dpnebert/Dura-M3000/firmware/components/dura_board/dura_lcd_assets.c

// Generated from Dura legacy MikroBasic reference assets.
// Source directory: /home/omi/work_projects/dura/AVR/reference_source/Release_1_1_3/Src/Meter_Project
// Do not hand-edit byte data; regenerate from the reference source if assets change.

#include "dura_lcd_assets.h"

// Source: Graphics.mbas const QRcodeData as byte[((128*64)/8)] (1024 values)
const uint8_t dura_asset_QRcodeData[1024] = {
    0x00u, 0x00u, 0x00u, 0x00u, 0x00u, 0x00u, 0x00u, 0x00u, 0x00u, 0x00u, 0x00u, 0x00u, 0x00u, 0x00u, 0x00u, 0x00u,
    0x00u, 0x00u, 0x00u, 0x00u, 0x00u, 0x00u, 0x00u, 0x00u, 0x00u, 0x00u, 0x00u, 0x00u, 0x00u, 0x00u, 0x00u, 0x00u,
    0x00u, 0x00u, 0x00u, 0x00u, 0x00u, 0x00u, 0x00u, 0x80u, 0x80u, 0x80u, 0x80u, 0x80u, 0x80u, 0x80u, 0x80u, 0x80u,
    0x80u, 0x80u, 0x80u, 0x80u, 0x80u, 0x00u, 0x00u, 0x80u, 0x80u, 0x80u, 0x80u, 0x80u, 0x80u, 0x00u, 0x00u, 0x00u,
    0x00u, 0x80u, 0x80u, 0x00u, 0x00u, 0x00u, 0x00u, 0x00u, 0x00u, 0x00u, 0x00u, 0x80u, 0x80u, 0x80u, 0x80u, 0x80u,
    0x80u, 0x80u, 0x80u, 0x80u, 0x80u, 0x80u, 0x80u, 0x80u, 0x80u, 0x00u, 0x00u, 0x00u, 0x00u, 0x00u, 0x00u, 0x00u,
    0x00u, 0x00u, 0x00u, 0x00u, 0x00u, 0x00u, 0x00u, 0x00u, 0x00u, 0x00u, 0x00u, 0x00u, 0x00u, 0x00u, 0x00u, 0x00u,
    0x00u, 0x00u, 0x00u, 0x00u, 0x00u, 0x00u, 0x00u, 0x00u, 0x00u, 0x00u, 0x00u, 0x00u, 0x00u, 0x00u, 0x00u, 0x00u,
    0x00u, 0x00u, 0x00u, 0x00u, 0x00u, 0x00u, 0x00u, 0x00u, 0x00u, 0x00u, 0x00u, 0x00u, 0x00u, 0x00u, 0x00u, 0x00u,
    0x00u, 0x00u, 0x00u, 0x00u, 0x00u, 0x00u, 0x00u, 0x00u, 0x00u, 0x00u, 0x00u, 0x00u, 0x00u, 0x00u, 0x00u, 0x00u,
    0x00u, 0x00u, 0x00u, 0x00u, 0x00u, 0x00u, 0x00u, 0xFFu, 0xFFu, 0x01u, 0x01u, 0xF9u, 0xF9u, 0xF9u, 0xF9u, 0xF9u,
    0xF9u, 0x01u, 0x01u, 0xFFu, 0xFFu, 0x00u, 0x00u, 0x01u, 0x01u, 0xF9u, 0xF9u, 0x1Fu, 0x1Fu, 0x78u, 0x78u, 0x60u,
    0x60u, 0x7Fu, 0x7Fu, 0x00u, 0x00u, 0x00u, 0x00u, 0xFEu, 0xFEu, 0x00u, 0x00u, 0xFFu, 0xFFu, 0x01u, 0x01u, 0xF9u,
    0xF9u, 0xF9u, 0xF9u, 0xF9u, 0xF9u, 0x01u, 0x01u, 0xFFu, 0xFFu, 0x00u, 0x00u, 0x00u, 0x00u, 0x00u, 0x00u, 0x00u,
    0x00u, 0x00u, 0x00u, 0x00u, 0x00u, 0x00u, 0x00u, 0x00u, 0x00u, 0x00u, 0x00u, 0x00u, 0x00u, 0x00u, 0x00u, 0x00u,
    0x00u, 0x00u, 0x00u, 0x00u, 0x00u, 0x00u, 0x00u, 0x00u, 0x00u, 0x00u, 0x00u, 0x00u, 0x00u, 0x00u, 0x00u, 0x00u,
    0x00u, 0x00u, 0x00u, 0x00u, 0x00u, 0x00u, 0x00u, 0x00u, 0x00u, 0x00u, 0x00u, 0x00u, 0x00u, 0x00u, 0x00u, 0x00u,
    0x00u, 0x00u, 0x00u, 0x00u, 0x00u, 0x00u, 0x00u, 0x00u, 0x00u, 0x00u, 0x00u, 0x00u, 0x00u, 0x00u, 0x00u, 0x00u,
    0x00u, 0x00u, 0x00u, 0x00u, 0x00u, 0x00u, 0x00u, 0x9Fu, 0x9Fu, 0x98u, 0x98u, 0x19u, 0x19u, 0x99u, 0x99u, 0x99u,
    0x99u, 0x18u, 0x18u, 0x9Fu, 0x9Fu, 0x00u, 0x00u, 0x78u, 0x78u, 0x01u, 0x01u, 0xF8u, 0xF8u, 0x66u, 0x66u, 0xF8u,
    0xF8u, 0x66u, 0x66u, 0x18u, 0x18u, 0x80u, 0x80u, 0x79u, 0x79u, 0x00u, 0x00u, 0x9Fu, 0x9Fu, 0x18u, 0x18u, 0x19u,
    0x19u, 0x19u, 0x19u, 0x19u, 0x19u, 0x18u, 0x18u, 0x9Fu, 0x9Fu, 0x00u, 0x00u, 0x00u, 0x00u, 0x00u, 0x00u, 0x00u,
    0x00u, 0x00u, 0x00u, 0x00u, 0x00u, 0x00u, 0x00u, 0x00u, 0x00u, 0x00u, 0x00u, 0x00u, 0x00u, 0x00u, 0x00u, 0x00u,
    0x00u, 0x00u, 0x00u, 0x00u, 0x00u, 0x00u, 0x00u, 0x00u, 0x00u, 0x00u, 0x00u, 0x00u, 0x00u, 0x00u, 0x00u, 0x00u,
    0x00u, 0x00u, 0x00u, 0x00u, 0x00u, 0x00u, 0x00u, 0x00u, 0x00u, 0x00u, 0x00u, 0x00u, 0x00u, 0x00u, 0x00u, 0x00u,
    0x00u, 0x00u, 0x00u, 0x00u, 0x00u, 0x00u, 0x00u, 0x00u, 0x00u, 0x00u, 0x00u, 0x00u, 0x00u, 0x00u, 0x00u, 0x00u,
    0x00u, 0x00u, 0x00u, 0x00u, 0x00u, 0x00u, 0x00u, 0x67u, 0x67u, 0xE7u, 0xE7u, 0xFEu, 0xFEu, 0x87u, 0x87u, 0x81u,
    0x81u, 0x66u, 0x66u, 0x99u, 0x99u, 0x18u, 0x18u, 0x98u, 0x98u, 0x86u, 0x86u, 0x9Fu, 0x9Fu, 0x7Eu, 0x7Eu, 0x81u,
    0x81u, 0x1Eu, 0x1Eu, 0x06u, 0x06u, 0x9Fu, 0x9Fu, 0x80u, 0x80u, 0x7Eu, 0x7Eu, 0x99u, 0x99u, 0x7Eu, 0x7Eu, 0x1Eu,
    0x1Eu, 0x7Eu, 0x7Eu, 0x66u, 0x66u, 0x66u, 0x66u, 0xF9u, 0xF9u, 0x00u, 0x00u, 0x00u, 0x00u, 0x00u, 0x00u, 0x00u,
    0x00u, 0x00u, 0x00u, 0x00u, 0x00u, 0x00u, 0x00u, 0x00u, 0x00u, 0x00u, 0x00u, 0x00u, 0x00u, 0x00u, 0x00u, 0x00u,
    0x00u, 0x00u, 0x00u, 0x00u, 0x00u, 0x00u, 0x00u, 0x00u, 0x00u, 0x00u, 0x00u, 0x00u, 0x00u, 0x00u, 0x00u, 0x00u,
    0x00u, 0x00u, 0x00u, 0x00u, 0x00u, 0x00u, 0x00u, 0x00u, 0x00u, 0x00u, 0x00u, 0x00u, 0x00u, 0x00u, 0x00u, 0x00u,
    0x00u, 0x00u, 0x00u, 0x00u, 0x00u, 0x00u, 0x00u, 0x00u, 0x00u, 0x00u, 0x00u, 0x00u, 0x00u, 0x00u, 0x00u, 0x00u,
    0x00u, 0x00u, 0x00u, 0x00u, 0x00u, 0x00u, 0x00u, 0xFEu, 0xFEu, 0x1Fu, 0x1Fu, 0x1Fu, 0x1Fu, 0x67u, 0x67u, 0x7Fu,
    0x7Fu, 0x86u, 0x86u, 0x99u, 0x99u, 0x9Eu, 0x9Eu, 0x81u, 0x81u, 0x81u, 0x81u, 0x81u, 0x81u, 0xE6u, 0xE6u, 0x79u,
    0x79u, 0x86u, 0x86u, 0x06u, 0x06u, 0x7Fu, 0x7Fu, 0x87u, 0x87u, 0xE0u, 0xE0u, 0xF9u, 0xF9u, 0xF8u, 0xF8u, 0xE6u,
    0xE6u, 0x18u, 0x18u, 0xF8u, 0xF8u, 0x9Eu, 0x9Eu, 0x79u, 0x79u, 0x00u, 0x00u, 0x00u, 0x00u, 0x00u, 0x00u, 0x00u,
    0x00u, 0x00u, 0x00u, 0x00u, 0x00u, 0x00u, 0x00u, 0x00u, 0x00u, 0x00u, 0x00u, 0x00u, 0x00u, 0x00u, 0x00u, 0x00u,
    0x00u, 0x00u, 0x00u, 0x00u, 0x00u, 0x00u, 0x00u, 0x00u, 0x00u, 0x00u, 0x00u, 0x00u, 0x00u, 0x00u, 0x00u, 0x00u,
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
};

// Source: Graphics.mbas const durametertitle_bmp_glcd_bmp as byte[((128*8)/8)] (128 values)
const uint8_t dura_asset_durametertitle_bmp_glcd_bmp[128] = {
    0x00u, 0x00u, 0x00u, 0x00u, 0x00u, 0x00u, 0x00u, 0x00u, 0x00u, 0xFFu, 0xFFu, 0xFFu, 0x81u, 0x81u, 0x81u, 0xFFu,
    0xFFu, 0x7Eu, 0x00u, 0x00u, 0x00u, 0x7Eu, 0xFEu, 0xFEu, 0x80u, 0x80u, 0x80u, 0xFEu, 0xFEu, 0xFEu, 0x00u, 0x00u,
    0xFEu, 0xFEu, 0xFEu, 0x08u, 0x06u, 0x06u, 0x06u, 0x06u, 0x00u, 0x60u, 0xF4u, 0xF6u, 0x96u, 0x96u, 0x96u, 0xFEu,
    0xFCu, 0xF8u, 0x00u, 0x00u, 0x00u, 0x10u, 0x10u, 0x10u, 0x10u, 0x10u, 0x10u, 0x10u, 0x10u, 0x00u, 0x00u, 0x00u,
    0xFFu, 0xFFu, 0xFFu, 0x07u, 0x0Eu, 0x1Cu, 0x38u, 0x38u, 0x1Cu, 0x0Eu, 0x07u, 0xFFu, 0xFFu, 0xFFu, 0x00u, 0x00u,
    0x00u, 0x7Cu, 0xFEu, 0xFEu, 0x96u, 0x96u, 0x96u, 0x9Eu, 0xDCu, 0x00u, 0x00u, 0x00u, 0x06u, 0x06u, 0x7Fu, 0xFFu,
    0xFFu, 0x86u, 0x86u, 0x00u, 0x00u, 0x00u, 0x7Cu, 0xFEu, 0xFEu, 0x96u, 0x96u, 0x96u, 0x9Eu, 0xDCu, 0x00u, 0x00u,
    0x00u, 0xFEu, 0xFEu, 0xFEu, 0x0Cu, 0x06u, 0x06u, 0x06u, 0x06u, 0x00u, 0x00u, 0x00u, 0x00u, 0x00u, 0x00u, 0x00u
};

// Source: Graphics.mbas const logoData as byte[((128*64)/8)] (1024 values)
const uint8_t dura_asset_logoData[1024] = {
    0x00u, 0x00u, 0x00u, 0x00u, 0x00u, 0x00u, 0x00u, 0x00u, 0x00u, 0x00u, 0x00u, 0x00u, 0x00u, 0x00u, 0xFEu, 0xFCu,
    0xF8u, 0xF0u, 0xE0u, 0xC0u, 0x00u, 0x00u, 0x00u, 0x00u, 0x00u, 0x00u, 0x00u, 0x00u, 0x00u, 0x00u, 0x00u, 0x00u,
    0x00u, 0x00u, 0xFCu, 0xFCu, 0xFCu, 0x0Cu, 0x0Cu, 0x0Cu, 0x1Cu, 0xFCu, 0xF8u, 0xF0u, 0x00u, 0x00u, 0xF0u, 0xF0u,
    0x00u, 0x00u, 0x00u, 0xF0u, 0xF0u, 0x00u, 0x00u, 0xF0u, 0xF0u, 0x30u, 0x30u, 0x30u, 0x70u, 0xE0u, 0xC0u, 0x00u,
    0x00u, 0x00u, 0x00u, 0x80u, 0xE0u, 0xF0u, 0xF0u, 0xE0u, 0x80u, 0x00u, 0x00u, 0x00u, 0x00u, 0xFCu, 0xFCu, 0xFCu,
    0xF8u, 0xE0u, 0x80u, 0x00u, 0x00u, 0x00u, 0x80u, 0xE0u, 0xF8u, 0xFCu, 0xFCu, 0xFCu, 0x00u, 0x00u, 0xF0u, 0xF0u,
    0x30u, 0x30u, 0x30u, 0x30u, 0x00u, 0x30u, 0x30u, 0x30u, 0xF0u, 0xF0u, 0x30u, 0x30u, 0x30u, 0x00u, 0xF0u, 0xF0u,
    0x30u, 0x30u, 0x30u, 0x30u, 0x00u, 0xF0u, 0xF0u, 0x30u, 0x30u, 0x30u, 0x70u, 0xE0u, 0xC0u, 0x00u, 0x00u, 0x00u,
    0x00u, 0x00u, 0x00u, 0x00u, 0x00u, 0x00u, 0x00u, 0x00u, 0x00u, 0x00u, 0x00u, 0x00u, 0x00u, 0x00u, 0xFFu, 0xFFu,
    0xFFu, 0xFFu, 0xFFu, 0xFFu, 0x00u, 0x00u, 0xFEu, 0xFCu, 0xF8u, 0xF0u, 0xE0u, 0xC0u, 0x80u, 0x00u, 0x00u, 0x00u,
    0x00u, 0x00u, 0xFFu, 0xFFu, 0xFFu, 0xC0u, 0xC0u, 0xC0u, 0xE0u, 0xFFu, 0x7Fu, 0x3Fu, 0x00u, 0x00u, 0x7Fu, 0xFFu,
    0xC0u, 0xC0u, 0xC0u, 0xFFu, 0x7Fu, 0x00u, 0x00u, 0xFFu, 0xFFu, 0x0Eu, 0x0Eu, 0x1Eu, 0x7Fu, 0xF3u, 0xC1u, 0x00u,
    0x00u, 0xE0u, 0xFCu, 0x7Fu, 0x1Fu, 0x18u, 0x18u, 0x1Fu, 0x7Fu, 0xFCu, 0xE0u, 0x00u, 0x00u, 0xFFu, 0xFFu, 0xFFu,
    0x01u, 0x07u, 0x1Fu, 0x7Eu, 0x7Cu, 0x7Eu, 0x1Fu, 0x07u, 0x01u, 0xFFu, 0xFFu, 0xFFu, 0x00u, 0x00u, 0xFFu, 0xFFu,
    0xC6u, 0xC6u, 0xC6u, 0xC0u, 0x00u, 0x00u, 0x00u, 0x00u, 0xFFu, 0xFFu, 0x00u, 0x00u, 0x00u, 0x00u, 0xFFu, 0xFFu,
    0xC6u, 0xC6u, 0xC6u, 0xC0u, 0x00u, 0xFFu, 0xFFu, 0x0Eu, 0x0Eu, 0x1Eu, 0x7Fu, 0xF3u, 0xC1u, 0x00u, 0x00u, 0x00u,
    0x00u, 0x00u, 0x00u, 0x00u, 0x00u, 0x00u, 0x00u, 0x00u, 0x80u, 0xC0u, 0x60u, 0x20u, 0x00u, 0x00u, 0xFFu, 0xFFu,
    0xFFu, 0xFFu, 0xFFu, 0xFFu, 0x00u, 0x00u, 0xFFu, 0xFFu, 0xFFu, 0xFFu, 0xFFu, 0xFFu, 0xFFu, 0x00u, 0xFEu, 0xFCu,
    0xF8u, 0xF0u, 0xE0u, 0xC0u, 0x80u, 0x00u, 0x00u, 0x00u, 0x0Cu, 0x0Cu, 0x0Cu, 0x0Cu, 0x0Cu, 0x0Cu, 0x0Cu, 0x0Cu,
    0x0Cu, 0x0Cu, 0x0Cu, 0x0Cu, 0x0Cu, 0x0Cu, 0x0Cu, 0x0Cu, 0x0Cu, 0x0Cu, 0x0Cu, 0x0Cu, 0x0Cu, 0x0Cu, 0x0Cu, 0x0Cu,
    0x0Cu, 0x0Cu, 0x0Cu, 0x0Cu, 0x0Cu, 0x0Cu, 0x0Cu, 0x0Cu, 0x0Cu, 0x0Cu, 0x0Cu, 0x0Cu, 0x0Cu, 0x0Cu, 0x0Cu, 0x0Cu,
    0x0Cu, 0x0Cu, 0x0Cu, 0x0Cu, 0x0Cu, 0x0Cu, 0x0Cu, 0x0Cu, 0x0Cu, 0x0Cu, 0x0Cu, 0x0Cu, 0x0Cu, 0x0Cu, 0x0Cu, 0x0Cu,
    0x0Cu, 0x0Cu, 0x0Cu, 0x0Cu, 0x0Cu, 0x0Cu, 0x0Cu, 0x0Cu, 0x0Cu, 0x0Cu, 0x0Cu, 0x0Cu, 0x0Cu, 0x0Cu, 0x0Cu, 0x0Cu,
    0x0Cu, 0x0Cu, 0x0Cu, 0x0Cu, 0x0Cu, 0x0Cu, 0x0Cu, 0x0Cu, 0x00u, 0x00u, 0x00u, 0x00u, 0x00u, 0x00u, 0x00u, 0x00u,
    0x00u, 0x00u, 0xC0u, 0xF0u, 0x18u, 0xCCu, 0xE6u, 0xFBu, 0xFDu, 0xFEu, 0x06u, 0x01u, 0x00u, 0x00u, 0xFFu, 0xFFu,
    0xFFu, 0xFFu, 0xFFu, 0xFFu, 0x00u, 0x00u, 0xFFu, 0xFFu, 0xFFu, 0xFFu, 0xFFu, 0xFFu, 0xFFu, 0x00u, 0xFFu, 0xFFu,
    0xFFu, 0xFFu, 0xFFu, 0xFFu, 0xFFu, 0x00u, 0x00u, 0x01u, 0xE6u, 0xCCu, 0x18u, 0x60u, 0x80u, 0x00u, 0x00u, 0x00u,
    0x00u, 0x00u, 0x00u, 0x00u, 0x01u, 0x01u, 0x7Fu, 0x01u, 0x01u, 0x00u, 0x38u, 0x54u, 0x54u, 0x2Cu, 0x00u, 0x38u,
    0x44u, 0x44u, 0x44u, 0x00u, 0x7Fu, 0x04u, 0x04u, 0x78u, 0x00u, 0x7Cu, 0x04u, 0x04u, 0x78u, 0x00u, 0x38u, 0x44u,
    0x44u, 0x38u, 0x00u, 0x7Fu, 0x00u, 0x38u, 0x44u, 0x44u, 0x38u, 0x00u, 0x38u, 0x44u, 0x44u, 0xFCu, 0x00u, 0x0Cu,
    0xB0u, 0x60u, 0x18u, 0x04u, 0x00u, 0x00u, 0x00u, 0x3Cu, 0x60u, 0x1Cu, 0x60u, 0x3Cu, 0x00u, 0x00u, 0x7Du, 0x00u,
    0x04u, 0x7Fu, 0x04u, 0x00u, 0x7Fu, 0x04u, 0x04u, 0x78u, 0x00u, 0x00u, 0x00u, 0x00u, 0x00u, 0x00u, 0x00u, 0x00u,
    0xF0u, 0x7Fu, 0x03u, 0xF8u, 0xFFu, 0xFFu, 0xFFu, 0xFFu, 0xFFu, 0xFFu, 0xF8u, 0xE0u, 0x80u, 0x00u, 0x07u, 0x0Fu,
    0x1Fu, 0x3Fu, 0xFFu, 0xFFu, 0x00u, 0x00u, 0xFFu, 0xFFu, 0xFFu, 0xFFu, 0xFFu, 0xFFu, 0xFFu, 0x00u, 0xFFu, 0xFFu,
    0xFFu, 0xFFu, 0xFFu, 0xFFu, 0xFFu, 0x00u, 0x00u, 0x00u, 0x0Fu, 0xFFu, 0xFFu, 0xF8u, 0x03u, 0x7Eu, 0xE0u, 0x00u,
    0x00u, 0x00u, 0x00u, 0x00u, 0x00u, 0x00u, 0x00u, 0x00u, 0x00u, 0x00u, 0xF0u, 0x00u, 0x00u, 0x00u, 0x00u, 0x80u,
    0x40u, 0x40u, 0xC0u, 0x00u, 0x80u, 0x40u, 0x40u, 0x00u, 0x40u, 0xF0u, 0x40u, 0x00u, 0x00u, 0xD0u, 0x00u, 0xC0u,
    0x40u, 0x40u, 0x80u, 0x00u, 0x80u, 0x40u, 0x40u, 0xC0u, 0x00u, 0x00u, 0x01u, 0x01u, 0x71u, 0x80u, 0x00u, 0x80u,
    0x73u, 0x00u, 0x80u, 0x40u, 0x40u, 0xC0u, 0x00u, 0xF0u, 0x00u, 0xC0u, 0x00u, 0x00u, 0xC0u, 0x00u, 0x80u, 0x40u,
    0x40u, 0xC0u, 0x00u, 0x00u, 0x00u, 0x00u, 0x00u, 0x00u, 0x00u, 0x00u, 0x00u, 0x00u, 0x00u, 0x00u, 0x00u, 0x00u,
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
};

// Source: Graphics.mbas const battery_icon_glcd_bmp as byte[(32*15)/8] (60 values)
const uint8_t dura_asset_battery_icon_glcd_bmp[60] = {
    0xF8u, 0x04u, 0x04u, 0x04u, 0x07u, 0x47u, 0x47u, 0xF7u, 0x47u, 0x47u, 0x07u, 0x04u, 0x04u, 0x04u, 0xF8u, 0xFFu,
    0x00u, 0x00u, 0x00u, 0x80u, 0xC0u, 0xE0u, 0xF1u, 0xB8u, 0x98u, 0x8Cu, 0x82u, 0x00u, 0x00u, 0xFFu, 0xFFu, 0x00u,
    0x80u, 0xC0u, 0x70u, 0x38u, 0x1Cu, 0x0Eu, 0x07u, 0x03u, 0x01u, 0x00u, 0x00u, 0x00u, 0xFFu, 0x7Fu, 0x80u, 0x81u,
    0x80u, 0x80u, 0x90u, 0x90u, 0x90u, 0x90u, 0x90u, 0x80u, 0x80u, 0x80u, 0x80u, 0x7Fu
};

// Source: Graphics.mbas const thick_glcd_bmp as byte[17] (17 values)
const uint8_t dura_asset_thick_glcd_bmp[17] = {
    0x01u, 0x1Fu, 0x01u, 0x00u, 0x1Fu, 0x04u, 0x1Cu, 0x00u, 0x1Du, 0x00u, 0x1Cu, 0x14u, 0x14u, 0x00u, 0x1Fu, 0x08u,
    0x14u
};

// Source: Graphics.mbas const thin_glcd_bmp as byte[13] (13 values)
const uint8_t dura_asset_thin_glcd_bmp[13] = {
    0x01u, 0x1Fu, 0x01u, 0x00u, 0x1Fu, 0x04u, 0x1Cu, 0x00u, 0x1Du, 0x00u, 0x1Cu, 0x04u, 0x18u
};

// Source: Graphics.mbas const thick_pointer as byte[7] (7 values)
const uint8_t dura_asset_thick_pointer[7] = {
    0x11u, 0x1Bu, 0x1Fu, 0x1Fu, 0x1Fu, 0x0Eu, 0x04u
};

// Source: Dan-approved 2026-09-09 calibration-progress proposal.
// Eight 23x23 page-packed wheel frames; phase advances only with flow counts.
const uint8_t dura_asset_calibration_wheel_frames[8][69] = {
    /* phase 0 */ {
        0x00u, 0xC0u, 0x20u, 0x18u, 0x08u, 0x04u, 0x12u, 0x7Au, 0xF1u, 0xC1u, 0x01u, 0x01u,
        0x01u, 0x01u, 0x01u, 0x02u, 0x02u, 0x04u, 0x08u, 0x18u, 0x20u, 0xC0u, 0x00u, 0x7Fu,
        0x80u, 0x00u, 0x00u, 0x00u, 0x00u, 0x00u, 0x00u, 0x81u, 0xE3u, 0xFDu, 0x3Cu, 0x1Cu,
        0x18u, 0x18u, 0x18u, 0x18u, 0x18u, 0x18u, 0x1Cu, 0x1Cu, 0x9Cu, 0x7Fu, 0x00u, 0x01u,
        0x02u, 0x0Cu, 0x08u, 0x10u, 0x20u, 0x22u, 0x47u, 0x43u, 0x40u, 0x40u, 0x40u, 0x40u,
        0x40u, 0x20u, 0x20u, 0x10u, 0x08u, 0x0Cu, 0x02u, 0x01u, 0x00u,
    },
    /* phase 1 */ {
        0x00u, 0xC0u, 0x20u, 0x18u, 0x08u, 0x04u, 0x02u, 0x02u, 0x01u, 0x39u, 0xF9u, 0x81u,
        0x01u, 0x01u, 0x01u, 0x02u, 0x02u, 0x04u, 0x08u, 0x18u, 0x20u, 0xC0u, 0x00u, 0x7Fu,
        0x80u, 0x00u, 0x00u, 0x00u, 0x80u, 0xC0u, 0xE0u, 0x70u, 0x38u, 0x1Fu, 0x1Fu, 0x1Cu,
        0x30u, 0x20u, 0x20u, 0x40u, 0x40u, 0xE0u, 0xE0u, 0xE0u, 0x80u, 0x7Fu, 0x00u, 0x01u,
        0x02u, 0x0Cu, 0x08u, 0x10u, 0x21u, 0x20u, 0x40u, 0x40u, 0x40u, 0x40u, 0x40u, 0x40u,
        0x40u, 0x20u, 0x20u, 0x10u, 0x08u, 0x0Cu, 0x02u, 0x01u, 0x00u,
    },
    /* phase 2 */ {
        0x00u, 0xC0u, 0x20u, 0x18u, 0x08u, 0x04u, 0x02u, 0x02u, 0x01u, 0x01u, 0x01u, 0x81u,
        0xF9u, 0x39u, 0x01u, 0x02u, 0x02u, 0x04u, 0x08u, 0x18u, 0x20u, 0xC0u, 0x00u, 0x7Fu,
        0x80u, 0x00u, 0x30u, 0x10u, 0x10u, 0x10u, 0x10u, 0x10u, 0x18u, 0x1Cu, 0x1Fu, 0x3Fu,
        0x70u, 0xE0u, 0xC0u, 0x80u, 0x00u, 0x00u, 0x00u, 0x00u, 0x80u, 0x7Fu, 0x00u, 0x01u,
        0x02u, 0x0Cu, 0x08u, 0x10u, 0x20u, 0x20u, 0x40u, 0x40u, 0x40u, 0x40u, 0x40u, 0x40u,
        0x40u, 0x21u, 0x27u, 0x17u, 0x0Fu, 0x0Cu, 0x02u, 0x01u, 0x00u,
    },
    /* phase 3 */ {
        0x00u, 0xC0u, 0x20u, 0x18u, 0x08u, 0x04u, 0x02u, 0x02u, 0x01u, 0x01u, 0x01u, 0x01u,
        0x01u, 0x81u, 0xC1u, 0xE2u, 0x42u, 0x04u, 0x08u, 0x18u, 0x20u, 0xC0u, 0x00u, 0x7Fu,
        0x80u, 0x00u, 0x06u, 0x04u, 0x04u, 0x04u, 0x04u, 0x04u, 0x0Cu, 0x1Cu, 0x1Eu, 0x7Fu,
        0xE3u, 0x81u, 0x00u, 0x00u, 0x00u, 0x00u, 0x00u, 0x00u, 0x80u, 0x7Fu, 0x00u, 0x01u,
        0x02u, 0x0Cu, 0x08u, 0x10u, 0x20u, 0x20u, 0x40u, 0x40u, 0x40u, 0x40u, 0x40u, 0x5Du,
        0x5Fu, 0x3Eu, 0x20u, 0x10u, 0x08u, 0x0Cu, 0x02u, 0x01u, 0x00u,
    },
    /* phase 4 */ {
        0x00u, 0xC0u, 0x20u, 0x98u, 0xC8u, 0x84u, 0x82u, 0x02u, 0x01u, 0x01u, 0x01u, 0x01u,
        0x01u, 0x01u, 0x01u, 0x02u, 0x02u, 0x84u, 0x08u, 0x18u, 0x20u, 0xC0u, 0x00u, 0x7Fu,
        0x80u, 0x00u, 0x00u, 0x00u, 0x01u, 0x03u, 0x03u, 0x06u, 0x02u, 0x1Cu, 0xFCu, 0xFCu,
        0x0Cu, 0x06u, 0x07u, 0x03u, 0x01u, 0x01u, 0x00u, 0x00u, 0x80u, 0x7Fu, 0x00u, 0x01u,
        0x02u, 0x0Cu, 0x08u, 0x10u, 0x20u, 0x20u, 0x40u, 0x40u, 0x78u, 0x7Fu, 0x7Fu, 0x40u,
        0x40u, 0x20u, 0x20u, 0x10u, 0x08u, 0x0Cu, 0x02u, 0x01u, 0x00u,
    },
    /* phase 5 */ {
        0x00u, 0xC0u, 0x20u, 0x18u, 0x08u, 0x24u, 0x72u, 0xE2u, 0xC1u, 0x81u, 0x01u, 0x01u,
        0x01u, 0x01u, 0x01u, 0x02u, 0x02u, 0x04u, 0x08u, 0x18u, 0x20u, 0xC0u, 0x00u, 0x7Fu,
        0x80u, 0x00u, 0x00u, 0x00u, 0x00u, 0x00u, 0x00u, 0x01u, 0x83u, 0xFDu, 0x7Cu, 0x1Cu,
        0x18u, 0x08u, 0x08u, 0x08u, 0x08u, 0x08u, 0x0Cu, 0x00u, 0x80u, 0x7Fu, 0x00u, 0x01u,
        0x02u, 0x0Cu, 0x08u, 0x10u, 0x20u, 0x3Cu, 0x5Eu, 0x5Fu, 0x41u, 0x40u, 0x40u, 0x40u,
        0x40u, 0x20u, 0x20u, 0x10u, 0x08u, 0x0Cu, 0x02u, 0x01u, 0x00u,
    },
    /* phase 6 */ {
        0x00u, 0xC0u, 0x20u, 0x18u, 0x08u, 0x04u, 0x02u, 0x02u, 0x39u, 0xF9u, 0x81u, 0x01u,
        0x01u, 0x01u, 0x01u, 0x02u, 0x02u, 0x04u, 0x08u, 0x18u, 0x20u, 0xC0u, 0x00u, 0x7Fu,
        0x80u, 0x00u, 0x00u, 0x00u, 0x00u, 0x80u, 0xC0u, 0xE0u, 0x73u, 0x3Fu, 0x1Cu, 0x1Cu,
        0x30u, 0x20u, 0x20u, 0x20u, 0x20u, 0x20u, 0x60u, 0x00u, 0x80u, 0x7Fu, 0x00u, 0x01u,
        0x02u, 0x0Cu, 0x0Fu, 0x17u, 0x27u, 0x21u, 0x40u, 0x40u, 0x40u, 0x40u, 0x40u, 0x40u,
        0x40u, 0x20u, 0x20u, 0x10u, 0x08u, 0x0Cu, 0x02u, 0x01u, 0x00u,
    },
    /* phase 7 */ {
        0x00u, 0xC0u, 0x20u, 0x18u, 0x08u, 0x04u, 0x02u, 0x02u, 0x01u, 0x01u, 0x81u, 0xF9u,
        0x39u, 0x01u, 0x01u, 0x02u, 0x02u, 0x04u, 0x08u, 0x18u, 0x20u, 0xC0u, 0x00u, 0x7Fu,
        0x80u, 0xE0u, 0xE0u, 0xE0u, 0x20u, 0x20u, 0x10u, 0x10u, 0x18u, 0x1Fu, 0x1Fu, 0x1Cu,
        0x20u, 0x70u, 0xE0u, 0xC0u, 0x80u, 0x00u, 0x00u, 0x00u, 0x80u, 0x7Fu, 0x00u, 0x01u,
        0x02u, 0x0Cu, 0x08u, 0x10u, 0x20u, 0x20u, 0x40u, 0x40u, 0x40u, 0x40u, 0x40u, 0x40u,
        0x40u, 0x20u, 0x21u, 0x13u, 0x09u, 0x0Cu, 0x02u, 0x01u, 0x00u,
    },
};

// Source: gLCDfont.mbas const font as byte[255*5] (1275 values)
const uint8_t dura_asset_font[1275] = {
    0x00u, 0x00u, 0x00u, 0x00u, 0x00u, 0x7Cu, 0xDAu, 0xF2u, 0xDAu, 0x7Cu, 0x7Cu, 0xD6u, 0xF2u, 0xD6u, 0x7Cu, 0x38u,
    0x7Cu, 0x3Eu, 0x7Cu, 0x38u, 0x18u, 0x3Cu, 0x7Eu, 0x3Cu, 0x18u, 0x38u, 0xEAu, 0xBEu, 0xEAu, 0x38u, 0x38u, 0x7Au,
    0xFEu, 0x7Au, 0x38u, 0x00u, 0x18u, 0x3Cu, 0x18u, 0x00u, 0xFFu, 0xE7u, 0xC3u, 0xE7u, 0xFFu, 0x00u, 0x18u, 0x24u,
    0x18u, 0x00u, 0xFFu, 0xE7u, 0xDBu, 0xE7u, 0xFFu, 0x0Cu, 0x12u, 0x5Cu, 0x60u, 0x70u, 0x64u, 0x94u, 0x9Eu, 0x94u,
    0x64u, 0x02u, 0xFEu, 0xA0u, 0xA0u, 0xE0u, 0x02u, 0xFEu, 0xA0u, 0xA4u, 0xFCu, 0x5Au, 0x3Cu, 0xE7u, 0x3Cu, 0x5Au,
    0xFEu, 0x7Cu, 0x38u, 0x38u, 0x10u, 0x10u, 0x38u, 0x38u, 0x7Cu, 0xFEu, 0x28u, 0x44u, 0xFEu, 0x44u, 0x28u, 0xFAu,
    0xFAu, 0x00u, 0xFAu, 0xFAu, 0x60u, 0x90u, 0xFEu, 0x80u, 0xFEu, 0x00u, 0x66u, 0x91u, 0xA9u, 0x56u, 0x06u, 0x06u,
    0x06u, 0x06u, 0x06u, 0x29u, 0x45u, 0xFFu, 0x45u, 0x29u, 0x10u, 0x20u, 0x7Eu, 0x20u, 0x10u, 0x08u, 0x04u, 0x7Eu,
    0x04u, 0x08u, 0x10u, 0x10u, 0x54u, 0x38u, 0x10u, 0x10u, 0x38u, 0x54u, 0x10u, 0x10u, 0x78u, 0x08u, 0x08u, 0x08u,
    0x08u, 0x30u, 0x78u, 0x30u, 0x78u, 0x30u, 0x0Cu, 0x1Cu, 0x7Cu, 0x1Cu, 0x0Cu, 0x60u, 0x70u, 0x7Cu, 0x70u, 0x60u,
    0x00u, 0x00u, 0x00u, 0x00u, 0x00u, 0x00u, 0x00u, 0xFAu, 0x00u, 0x00u, 0x00u, 0xE0u, 0x00u, 0xE0u, 0x00u, 0x28u,
    0xFEu, 0x28u, 0xFEu, 0x28u, 0x24u, 0x54u, 0xFEu, 0x54u, 0x48u, 0xC4u, 0xC8u, 0x10u, 0x26u, 0x46u, 0x6Cu, 0x92u,
    0x6Au, 0x04u, 0x0Au, 0x00u, 0x10u, 0xE0u, 0xC0u, 0x00u, 0x00u, 0x38u, 0x44u, 0x82u, 0x00u, 0x00u, 0x82u, 0x44u,
    0x38u, 0x00u, 0x54u, 0x38u, 0xFEu, 0x38u, 0x54u, 0x10u, 0x10u, 0x7Cu, 0x10u, 0x10u, 0x00u, 0x01u, 0x0Eu, 0x0Cu,
    0x00u, 0x10u, 0x10u, 0x10u, 0x10u, 0x10u, 0x00u, 0x00u, 0x06u, 0x06u, 0x00u, 0x04u, 0x08u, 0x10u, 0x20u, 0x40u,
    0x7Cu, 0x8Au, 0x92u, 0xA2u, 0x7Cu, 0x00u, 0x42u, 0xFEu, 0x02u, 0x00u, 0x4Eu, 0x92u, 0x92u, 0x92u, 0x62u, 0x84u,
    0x82u, 0x92u, 0xB2u, 0xCCu, 0x18u, 0x28u, 0x48u, 0xFEu, 0x08u, 0xE4u, 0xA2u, 0xA2u, 0xA2u, 0x9Cu, 0x3Cu, 0x52u,
    0x92u, 0x92u, 0x8Cu, 0x82u, 0x84u, 0x88u, 0x90u, 0xE0u, 0x6Cu, 0x92u, 0x92u, 0x92u, 0x6Cu, 0x62u, 0x92u, 0x92u,
    0x94u, 0x78u, 0x00u, 0x00u, 0x28u, 0x00u, 0x00u, 0x00u, 0x02u, 0x2Cu, 0x00u, 0x00u, 0x00u, 0x10u, 0x28u, 0x44u,
    0x82u, 0x28u, 0x28u, 0x28u, 0x28u, 0x28u, 0x00u, 0x82u, 0x44u, 0x28u, 0x10u, 0x40u, 0x80u, 0x9Au, 0x90u, 0x60u,
    0x7Cu, 0x82u, 0xBAu, 0x9Au, 0x72u, 0x3Eu, 0x48u, 0x88u, 0x48u, 0x3Eu, 0xFEu, 0x92u, 0x92u, 0x92u, 0x6Cu, 0x7Cu,
    0x82u, 0x82u, 0x82u, 0x44u, 0xFEu, 0x82u, 0x82u, 0x82u, 0x7Cu, 0xFEu, 0x92u, 0x92u, 0x92u, 0x82u, 0xFEu, 0x90u,
    0x90u, 0x90u, 0x80u, 0x7Cu, 0x82u, 0x82u, 0x8Au, 0xCEu, 0xFEu, 0x10u, 0x10u, 0x10u, 0xFEu, 0x00u, 0x82u, 0xFEu,
    0x82u, 0x00u, 0x04u, 0x02u, 0x82u, 0xFCu, 0x80u, 0xFEu, 0x10u, 0x28u, 0x44u, 0x82u, 0xFEu, 0x02u, 0x02u, 0x02u,
    0x02u, 0xFEu, 0x40u, 0x38u, 0x40u, 0xFEu, 0xFEu, 0x20u, 0x10u, 0x08u, 0xFEu, 0x7Cu, 0x82u, 0x82u, 0x82u, 0x7Cu,
    0xFEu, 0x90u, 0x90u, 0x90u, 0x60u, 0x7Cu, 0x82u, 0x8Au, 0x84u, 0x7Au, 0xFEu, 0x90u, 0x98u, 0x94u, 0x62u, 0x64u,
    0x92u, 0x92u, 0x92u, 0x4Cu, 0xC0u, 0x80u, 0xFEu, 0x80u, 0xC0u, 0xFCu, 0x02u, 0x02u, 0x02u, 0xFCu, 0xF8u, 0x04u,
    0x02u, 0x04u, 0xF8u, 0xFCu, 0x02u, 0x1Cu, 0x02u, 0xFCu, 0xC6u, 0x28u, 0x10u, 0x28u, 0xC6u, 0xC0u, 0x20u, 0x1Eu,
    0x20u, 0xC0u, 0x86u, 0x9Au, 0x92u, 0xB2u, 0xC2u, 0x00u, 0xFEu, 0x82u, 0x82u, 0x82u, 0x40u, 0x20u, 0x10u, 0x08u,
    0x04u, 0x00u, 0x82u, 0x82u, 0x82u, 0xFEu, 0x20u, 0x40u, 0x80u, 0x40u, 0x20u, 0x02u, 0x02u, 0x02u, 0x02u, 0x02u,
    0x00u, 0xC0u, 0xE0u, 0x10u, 0x00u, 0x04u, 0x2Au, 0x2Au, 0x1Eu, 0x02u, 0xFEu, 0x14u, 0x22u, 0x22u, 0x1Cu, 0x1Cu,
    0x22u, 0x22u, 0x22u, 0x14u, 0x1Cu, 0x22u, 0x22u, 0x14u, 0xFEu, 0x1Cu, 0x2Au, 0x2Au, 0x2Au, 0x18u, 0x00u, 0x10u,
    0x7Eu, 0x90u, 0x40u, 0x18u, 0x25u, 0x25u, 0x39u, 0x1Eu, 0xFEu, 0x10u, 0x20u, 0x20u, 0x1Eu, 0x00u, 0x22u, 0xBEu,
    0x02u, 0x00u, 0x04u, 0x02u, 0x02u, 0xBCu, 0x00u, 0xFEu, 0x08u, 0x14u, 0x22u, 0x00u, 0x00u, 0x82u, 0xFEu, 0x02u,
    0x00u, 0x3Eu, 0x20u, 0x1Eu, 0x20u, 0x1Eu, 0x3Eu, 0x10u, 0x20u, 0x20u, 0x1Eu, 0x1Cu, 0x22u, 0x22u, 0x22u, 0x1Cu,
    0x3Fu, 0x18u, 0x24u, 0x24u, 0x18u, 0x18u, 0x24u, 0x24u, 0x18u, 0x3Fu, 0x3Eu, 0x10u, 0x20u, 0x20u, 0x10u, 0x12u,
    0x2Au, 0x2Au, 0x2Au, 0x24u, 0x20u, 0x20u, 0xFCu, 0x22u, 0x24u, 0x3Cu, 0x02u, 0x02u, 0x04u, 0x3Eu, 0x38u, 0x04u,
    0x02u, 0x04u, 0x38u, 0x3Cu, 0x02u, 0x0Cu, 0x02u, 0x3Cu, 0x22u, 0x14u, 0x08u, 0x14u, 0x22u, 0x32u, 0x09u, 0x09u,
    0x09u, 0x3Eu, 0x22u, 0x26u, 0x2Au, 0x32u, 0x22u, 0x00u, 0x10u, 0x6Cu, 0x82u, 0x00u, 0x00u, 0x00u, 0xEEu, 0x00u,
    0x00u, 0x00u, 0x82u, 0x6Cu, 0x10u, 0x00u, 0x40u, 0x80u, 0x40u, 0x20u, 0x40u, 0x3Cu, 0x64u, 0xC4u, 0x64u, 0x3Cu,
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
};

// Source: fontComicSans7.mbas const comicSansMS7ptCharBitmaps as byte[(256-33)*11] (2453 values)
const uint8_t dura_asset_comicSansMS7ptCharBitmaps[2453] = {
    0x00u, 0x80u, 0x80u, 0x80u, 0x80u, 0x80u, 0x00u, 0x80u, 0x00u, 0x00u, 0x00u, 0x00u, 0xA0u, 0xA0u, 0xA0u, 0x00u,
    0x00u, 0x00u, 0x00u, 0x00u, 0x00u, 0x00u, 0x00u, 0x12u, 0x12u, 0xFFu, 0x24u, 0xFFu, 0x48u, 0x48u, 0x00u, 0x00u,
    0x00u, 0x20u, 0x78u, 0xA0u, 0xA0u, 0x70u, 0x28u, 0x28u, 0xF0u, 0x20u, 0x20u, 0x00u, 0x00u, 0xE4u, 0xA8u, 0xE8u,
    0x10u, 0x2Eu, 0x2Au, 0x4Eu, 0x00u, 0x00u, 0x00u, 0x00u, 0x30u, 0x50u, 0x60u, 0xA8u, 0xA8u, 0x90u, 0x68u, 0x00u,
    0x00u, 0x00u, 0x00u, 0x80u, 0x80u, 0x80u, 0x00u, 0x00u, 0x00u, 0x00u, 0x00u, 0x00u, 0x00u, 0x00u, 0x20u, 0x40u,
    0x80u, 0x80u, 0x80u, 0x80u, 0x80u, 0x40u, 0x20u, 0x00u, 0x00u, 0x80u, 0x40u, 0x20u, 0x20u, 0x20u, 0x20u, 0x20u,
    0x40u, 0x80u, 0x00u, 0x00u, 0x20u, 0xF8u, 0x20u, 0x50u, 0x00u, 0x00u, 0x00u, 0x00u, 0x00u, 0x00u, 0x00u, 0x00u,
    0x00u, 0x20u, 0x20u, 0xF8u, 0x20u, 0x20u, 0x00u, 0x00u, 0x00u, 0x00u, 0x00u, 0x00u, 0x00u, 0x00u, 0x00u, 0x00u,
    0x80u, 0x80u, 0x00u, 0x00u, 0x00u, 0x00u, 0x00u, 0x00u, 0x00u, 0xE0u, 0x00u, 0x00u, 0x00u, 0x00u, 0x00u, 0x00u,
    0x00u, 0x00u, 0x00u, 0x00u, 0x00u, 0x00u, 0x80u, 0x00u, 0x00u, 0x00u, 0x10u, 0x10u, 0x30u, 0x20u, 0x60u, 0x40u,
    0x80u, 0x80u, 0x00u, 0x00u, 0x00u, 0x00u, 0x60u, 0x90u, 0x90u, 0x90u, 0x90u, 0x90u, 0x60u, 0x00u, 0x00u, 0x00u,
    0x00u, 0xC0u, 0x40u, 0x40u, 0x40u, 0x40u, 0x40u, 0xE0u, 0x00u, 0x00u, 0x00u, 0x00u, 0x60u, 0x90u, 0x10u, 0x20u,
    0x40u, 0x80u, 0xF0u, 0x00u, 0x00u, 0x00u, 0x00u, 0x60u, 0x90u, 0x10u, 0x60u, 0x10u, 0x90u, 0x60u, 0x00u, 0x00u,
    0x00u, 0x00u, 0x10u, 0x30u, 0x50u, 0x50u, 0xF8u, 0x10u, 0x10u, 0x00u, 0x00u, 0x00u, 0x00u, 0xF0u, 0x80u, 0xE0u,
    0x90u, 0x10u, 0x90u, 0xE0u, 0x00u, 0x00u, 0x00u, 0x00u, 0x20u, 0x40u, 0xE0u, 0x90u, 0x90u, 0x90u, 0x60u, 0x00u,
    0x00u, 0x00u, 0x00u, 0xF8u, 0x10u, 0x10u, 0x20u, 0x20u, 0x40u, 0x40u, 0x00u, 0x00u, 0x00u, 0x00u, 0x60u, 0x90u,
    0x90u, 0x60u, 0x90u, 0x90u, 0x60u, 0x00u, 0x00u, 0x00u, 0x00u, 0x60u, 0x90u, 0x90u, 0x90u, 0x70u, 0x20u, 0x40u,
    0x00u, 0x00u, 0x00u, 0x00u, 0x00u, 0x00u, 0x80u, 0x00u, 0x00u, 0x80u, 0x00u, 0x00u, 0x00u, 0x00u, 0x00u, 0x00u,
    0x00u, 0x40u, 0x00u, 0x00u, 0x00u, 0x80u, 0x80u, 0x00u, 0x00u, 0x00u, 0x00u, 0x00u, 0x20u, 0x40u, 0xC0u, 0x20u,
    0x00u, 0x00u, 0x00u, 0x00u, 0x00u, 0x00u, 0x00u, 0xE0u, 0x00u, 0x00u, 0xE0u, 0x00u, 0x00u, 0x00u, 0x00u, 0x00u,
    0x00u, 0x00u, 0x80u, 0x40u, 0x60u, 0x80u, 0x00u, 0x00u, 0x00u, 0x00u, 0x00u, 0xE0u, 0x10u, 0x10u, 0x20u, 0x40u,
    0x00u, 0x40u, 0x00u, 0x00u, 0x00u, 0x00u, 0x38u, 0x46u, 0x92u, 0xAAu, 0xBEu, 0x40u, 0x3Cu, 0x00u, 0x00u, 0x00u,
    0x00u, 0x20u, 0x50u, 0x88u, 0x88u, 0xF8u, 0x88u, 0x88u, 0x00u, 0x00u, 0x00u, 0x00u, 0xE0u, 0x90u, 0x90u, 0xE0u,
    0x90u, 0x90u, 0xE0u, 0x00u, 0x00u, 0x00u, 0x00u, 0x70u, 0x88u, 0x80u, 0x80u, 0x80u, 0x88u, 0x70u, 0x00u, 0x00u,
    0x00u, 0x00u, 0xF0u, 0x88u, 0x88u, 0x88u, 0x88u, 0x88u, 0xF0u, 0x00u, 0x00u, 0x00u, 0x00u, 0xF8u, 0x80u, 0x80u,
    0xF8u, 0x80u, 0x80u, 0xF8u, 0x00u, 0x00u, 0x00u, 0x00u, 0xF0u, 0x80u, 0x80u, 0xF0u, 0x80u, 0x80u, 0x80u, 0x00u,
    0x00u, 0x00u, 0x00u, 0x78u, 0x84u, 0x80u, 0x9Cu, 0x84u, 0x84u, 0x78u, 0x00u, 0x00u, 0x00u, 0x00u, 0x84u, 0x84u,
    0x84u, 0xFCu, 0x84u, 0x84u, 0x84u, 0x00u, 0x00u, 0x00u, 0x00u, 0xE0u, 0x40u, 0x40u, 0x40u, 0x40u, 0x40u, 0xE0u,
    0x00u, 0x00u, 0x00u, 0x00u, 0x78u, 0x10u, 0x10u, 0x10u, 0x90u, 0x90u, 0x70u, 0x00u, 0x00u, 0x00u, 0x00u, 0x88u,
    0x90u, 0xA0u, 0xC0u, 0xC0u, 0xA0u, 0x98u, 0x00u, 0x00u, 0x00u, 0x00u, 0x80u, 0x80u, 0x80u, 0x80u, 0x80u, 0x80u,
    0xF0u, 0x00u, 0x00u, 0x00u, 0x00u, 0x82u, 0xC6u, 0xC6u, 0xAAu, 0xAAu, 0x92u, 0x92u, 0x00u, 0x00u, 0x00u, 0x00u,
    0x84u, 0xC4u, 0xC4u, 0xA4u, 0x94u, 0x8Cu, 0x84u, 0x00u, 0x00u, 0x00u, 0x00u, 0x78u, 0x84u, 0x84u, 0x84u, 0x84u,
    0x84u, 0x78u, 0x00u, 0x00u, 0x00u, 0x00u, 0xE0u, 0x90u, 0x90u, 0xE0u, 0x80u, 0x80u, 0x80u, 0x00u, 0x00u, 0x00u,
    0x00u, 0x38u, 0x44u, 0x82u, 0x82u, 0x82u, 0x4Au, 0x3Cu, 0x02u, 0x00u, 0x00u, 0x00u, 0xF0u, 0x88u, 0x88u, 0x90u,
    0xE0u, 0x90u, 0x88u, 0x00u, 0x00u, 0x00u, 0x00u, 0x70u, 0x88u, 0x80u, 0x70u, 0x08u, 0x88u, 0x70u, 0x00u, 0x00u,
    0x00u, 0x00u, 0xF8u, 0x20u, 0x20u, 0x20u, 0x20u, 0x20u, 0x20u, 0x00u, 0x00u, 0x00u, 0x00u, 0x88u, 0x88u, 0x88u,
    0x88u, 0x88u, 0x88u, 0x70u, 0x00u, 0x00u, 0x00u, 0x00u, 0x88u, 0x88u, 0x88u, 0x50u, 0x50u, 0x50u, 0x20u, 0x00u,
    0x00u, 0x00u, 0x00u, 0x92u, 0x92u, 0xAAu, 0xAAu, 0xC6u, 0x82u, 0x82u, 0x00u, 0x00u, 0x00u, 0x00u, 0x84u, 0x48u,
    0x30u, 0x30u, 0x30u, 0x48u, 0x84u, 0x00u, 0x00u, 0x00u, 0x00u, 0x88u, 0x48u, 0x50u, 0x30u, 0x20u, 0x20u, 0x40u,
    0x00u, 0x00u, 0x00u, 0x00u, 0xFCu, 0x08u, 0x10u, 0x20u, 0x40u, 0x80u, 0xFCu, 0x00u, 0x00u, 0x00u, 0x00u, 0xC0u,
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
};

// Source: fontComicSans7.mbas const comicSansMS7ptCharDescriptors as word[(256 - 33)*2] (446 values)
const uint16_t dura_asset_comicSansMS7ptCharDescriptors[446] = {
    1u, 0u, 3u, 11u, 8u, 22u, 5u, 33u, 7u, 44u, 5u, 55u,
    1u, 66u, 3u, 77u, 3u, 88u, 5u, 99u, 5u, 110u, 1u, 121u,
    3u, 132u, 1u, 143u, 4u, 154u, 4u, 165u, 3u, 176u, 4u, 187u,
    4u, 198u, 5u, 209u, 4u, 220u, 4u, 231u, 5u, 242u, 4u, 253u,
    4u, 264u, 1u, 275u, 2u, 286u, 3u, 297u, 3u, 308u, 3u, 319u,
    4u, 330u, 7u, 341u, 5u, 352u, 4u, 363u, 5u, 374u, 5u, 385u,
    5u, 396u, 4u, 407u, 6u, 418u, 6u, 429u, 3u, 440u, 5u, 451u,
    5u, 462u, 4u, 473u, 7u, 484u, 6u, 495u, 6u, 506u, 4u, 517u,
    7u, 528u, 5u, 539u, 5u, 550u, 5u, 561u, 5u, 572u, 5u, 583u,
    7u, 594u, 6u, 605u, 5u, 616u, 6u, 627u, 2u, 638u, 4u, 649u,
    2u, 660u, 4u, 671u, 6u, 682u, 2u, 693u, 4u, 704u, 4u, 715u,
    4u, 726u, 4u, 737u, 4u, 748u, 4u, 759u, 4u, 770u, 4u, 781u,
    1u, 792u, 3u, 803u, 4u, 814u, 1u, 825u, 5u, 836u, 4u, 847u,
    4u, 858u, 4u, 869u, 4u, 880u, 3u, 891u, 3u, 902u, 3u, 913u,
    4u, 924u, 3u, 935u, 5u, 946u, 5u, 957u, 5u, 968u, 4u, 979u,
    3u, 990u, 1u, 1001u, 3u, 1012u, 7u, 1023u, 7u, 1034u, 4u, 1045u,
    4u, 1045u, 4u, 1045u, 4u, 1045u, 4u, 1045u, 4u, 1045u, 4u, 1045u,
    4u, 1045u, 4u, 1045u, 4u, 1045u, 4u, 1045u, 4u, 1045u, 4u, 1045u,
    4u, 1045u, 4u, 1045u, 4u, 1045u, 4u, 1045u, 4u, 1045u, 4u, 1045u,
    4u, 1045u, 4u, 1045u, 4u, 1045u, 4u, 1045u, 4u, 1045u, 4u, 1045u,
    4u, 1045u, 4u, 1045u, 4u, 1045u, 4u, 1045u, 4u, 1045u, 4u, 1045u,
    4u, 1045u, 4u, 1045u, 2u, 1045u, 4u, 1045u, 4u, 1045u, 4u, 1045u,
    4u, 1045u, 4u, 1045u, 4u, 1045u, 4u, 1045u, 4u, 1045u, 4u, 1045u,
    4u, 1045u, 4u, 1045u, 4u, 1045u, 4u, 1045u, 4u, 1045u, 4u, 1045u,
    4u, 1045u, 4u, 1045u, 4u, 1045u, 4u, 1045u, 4u, 1045u, 4u, 1045u,
    4u, 1045u, 4u, 1045u, 4u, 1045u, 4u, 1045u, 4u, 1045u, 4u, 1045u,
    4u, 1045u, 4u, 1045u, 4u, 1045u, 4u, 1045u, 4u, 1045u, 4u, 1045u,
    4u, 1045u, 4u, 1045u, 4u, 1045u, 4u, 1045u, 4u, 1045u, 4u, 1045u,
    4u, 1045u, 4u, 1045u, 4u, 1045u, 4u, 1045u, 4u, 1045u, 4u, 1045u,
    4u, 1045u, 4u, 1045u, 4u, 1045u, 4u, 1045u, 4u, 1045u, 4u, 1045u,
    4u, 1045u, 4u, 1045u, 4u, 1045u, 4u, 1045u, 4u, 1045u, 4u, 1045u,
    4u, 1045u, 4u, 1045u, 4u, 1045u, 4u, 1045u, 4u, 1045u, 4u, 1045u,
    4u, 1045u, 4u, 1045u, 4u, 1045u, 4u, 1045u, 4u, 1045u, 4u, 1045u,
    4u, 1045u, 4u, 1045u, 4u, 1045u, 4u, 1045u, 4u, 1045u, 4u, 1045u,
    4u, 1045u, 4u, 1045u, 4u, 1045u, 4u, 1045u, 4u, 1045u, 4u, 1045u,
    4u, 1045u, 4u, 1045u, 4u, 1045u, 4u, 1045u, 4u, 1045u, 4u, 1045u,
    4u, 1045u, 4u, 1045u, 4u, 1045u, 4u, 1045u, 4u, 1045u, 4u, 1045u,
    4u, 1045u
};

// Genuine Comic Sans MS 6pt bitmap font for the 10-pixel Main Menu body.
// Raster source: Comic Sans MS Regular TTF, SHA-256 b82c53776058f291382ff7e008d4675839d2dc21eb295c66391f6fb0655d8fc0
// Rasterization: FreeType 2.14.3 monochrome hinted, 8 px em (6 pt at 96 dpi),
// fixed 10-row baseline cell. Glyphs are independently rasterized; no bitmap scaling.
const uint8_t dura_asset_comicSansMS6ptCharBitmaps[] = {
    0x00u, 0x00u, 0x80u, 0x80u, 0x80u, 0x80u, 0x00u, 0x80u, 0x00u, 0x00u, 0x00u, 0x00u,
    0xA0u, 0xA0u, 0xA0u, 0x00u, 0x00u, 0x00u, 0x00u, 0x00u, 0x00u, 0x00u, 0x14u, 0xFEu,
    0x2Cu, 0xFEu, 0x48u, 0x48u, 0x00u, 0x00u, 0x00u, 0x20u, 0x78u, 0xA0u, 0xF0u, 0x28u,
    0xA8u, 0xF0u, 0x20u, 0x00u, 0x00u, 0xD0u, 0xE0u, 0x20u, 0x3Cu, 0x54u, 0x5Cu, 0x00u,
    0x00u, 0x00u, 0x00u, 0x00u, 0x30u, 0x30u, 0x28u, 0xD8u, 0x98u, 0xE8u, 0x00u, 0x00u,
    0x00u, 0x00u, 0x80u, 0x80u, 0x80u, 0x00u, 0x00u, 0x00u, 0x00u, 0x00u, 0x00u, 0x00u,
    0x40u, 0x80u, 0x80u, 0x80u, 0x80u, 0x80u, 0x80u, 0x40u, 0x00u, 0x00u, 0x80u, 0x40u,
    0x20u, 0x20u, 0x20u, 0x20u, 0x40u, 0xC0u, 0x00u, 0x00u, 0x40u, 0xF0u, 0xA0u, 0x00u,
    0x00u, 0x00u, 0x00u, 0x00u, 0x00u, 0x00u, 0x00u, 0x00u, 0x40u, 0xE0u, 0x40u, 0x00u,
    0x00u, 0x00u, 0x00u, 0x00u, 0x00u, 0x00u, 0x00u, 0x00u, 0x00u, 0x80u, 0x80u, 0x00u,
    0x00u, 0x00u, 0x00u, 0x00u, 0x00u, 0xE0u, 0x00u, 0x00u, 0x00u, 0x00u, 0x00u, 0x00u,
    0x00u, 0x00u, 0x00u, 0x00u, 0x00u, 0x80u, 0x00u, 0x00u, 0x00u, 0x20u, 0x20u, 0x20u,
    0x40u, 0x40u, 0x80u, 0x80u, 0x00u, 0x00u, 0x00u, 0x00u, 0x70u, 0x88u, 0x88u, 0x88u,
    0x88u, 0x70u, 0x00u, 0x00u, 0x00u, 0x00u, 0xC0u, 0x40u, 0x40u, 0x40u, 0x40u, 0xE0u,
    0x00u, 0x00u, 0x00u, 0x00u, 0x60u, 0xA0u, 0x20u, 0x40u, 0x80u, 0xE0u, 0x00u, 0x00u,
    0x00u, 0x00u, 0xF0u, 0x10u, 0x60u, 0x10u, 0x90u, 0x60u, 0x00u, 0x00u, 0x00u, 0x00u,
    0x10u, 0x30u, 0x50u, 0xF8u, 0x10u, 0x10u, 0x00u, 0x00u, 0x00u, 0xF0u, 0x80u, 0xF0u,
    0x90u, 0x90u, 0xE0u, 0x00u, 0x00u, 0x00u, 0x00u, 0x00u, 0x20u, 0x40u, 0xF0u, 0x90u,
    0x90u, 0x60u, 0x00u, 0x00u, 0x00u, 0xF0u, 0x20u, 0x20u, 0x40u, 0x40u, 0x40u, 0x00u,
    0x00u, 0x00u, 0x00u, 0x70u, 0x90u, 0x60u, 0x90u, 0x90u, 0xE0u, 0x00u, 0x00u, 0x00u,
    0x00u, 0x00u, 0x60u, 0x90u, 0x90u, 0x70u, 0x20u, 0xC0u, 0x00u, 0x00u, 0x00u, 0x00u,
    0x00u, 0x00u, 0x80u, 0x00u, 0x80u, 0x00u, 0x00u, 0x00u, 0x00u, 0x00u, 0x00u, 0x00u,
    0x40u, 0x00u, 0x00u, 0x80u, 0x80u, 0x00u, 0x00u, 0x00u, 0x00u, 0x00u, 0x40u, 0x80u,
    0x40u, 0x00u, 0x00u, 0x00u, 0x00u, 0x00u, 0x00u, 0x00u, 0xE0u, 0x00u, 0xE0u, 0x00u,
    0x00u, 0x00u, 0x00u, 0x00u, 0x00u, 0x80u, 0x40u, 0x60u, 0x80u, 0x00u, 0x00u, 0x00u,
    0x00u, 0x00u, 0xE0u, 0x10u, 0x10u, 0x20u, 0x40u, 0x40u, 0x00u, 0x00u, 0x00u, 0x00u,
    0x78u, 0x4Cu, 0x94u, 0xA4u, 0xBCu, 0x40u, 0x38u, 0x00u, 0x00u, 0x00u, 0x10u, 0x10u,
    0x28u, 0x78u, 0x48u, 0x88u, 0x00u, 0x00u, 0x00u, 0x00u, 0xE0u, 0x90u, 0x90u, 0xE0u,
    0x90u, 0xE0u, 0x00u, 0x00u, 0x00u, 0x00u, 0x30u, 0x50u, 0x80u, 0x80u, 0x90u, 0x60u,
    0x00u, 0x00u, 0x00u, 0x00u, 0xC0u, 0xB0u, 0x88u, 0x88u, 0x88u, 0xF0u, 0x00u, 0x00u,
    0x00u, 0x00u, 0xF0u, 0x80u, 0x80u, 0xF0u, 0x80u, 0xF0u, 0x00u, 0x00u, 0x00u, 0x00u,
    0xF0u, 0x80u, 0xF0u, 0x80u, 0x80u, 0x80u, 0x00u, 0x00u, 0x00u, 0x00u, 0x38u, 0x40u,
    0xB8u, 0x88u, 0x90u, 0xF0u, 0x00u, 0x00u, 0x00u, 0x00u, 0x88u, 0x88u, 0xF8u, 0x88u,
    0x88u, 0x88u, 0x00u, 0x00u, 0x00u, 0x00u, 0xF8u, 0x20u, 0x20u, 0x20u, 0x20u, 0xF8u,
    0x00u, 0x00u, 0x00u, 0x00u, 0x78u, 0x10u, 0x10u, 0x10u, 0x90u, 0x70u, 0x00u, 0x00u,
    0x00u, 0x00u, 0x90u, 0xA0u, 0xC0u, 0xC0u, 0xA0u, 0x90u, 0x00u, 0x00u, 0x00u, 0x00u,
    0x80u, 0x80u, 0x80u, 0x80u, 0x80u, 0xE0u, 0x00u, 0x00u, 0x00u, 0x00u, 0x28u, 0x28u,
    0x78u, 0x74u, 0x74u, 0x94u, 0x00u, 0x00u, 0x00u, 0x00u, 0x88u, 0xC8u, 0xC8u, 0xA8u,
    0x98u, 0x88u, 0x00u, 0x00u, 0x00u, 0x00u, 0x38u, 0x44u, 0x84u, 0x84u, 0x88u, 0x78u,
    0x00u, 0x00u, 0x00u, 0x00u, 0xE0u, 0x90u, 0x90u, 0xE0u, 0x80u, 0x80u, 0x00u, 0x00u,
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
};

const uint16_t dura_asset_comicSansMS6ptCharDescriptors[] = {
    1u, 0u, // '!'
    3u, 10u, // '"'
    7u, 20u, // '#'
    5u, 30u, // '$'
    6u, 40u, // '%'
    5u, 50u, // '&'
    1u, 60u, // '\''
    2u, 70u, // '('
    3u, 80u, // ')'
    4u, 90u, // '*'
    3u, 100u, // '+'
    1u, 110u, // ','
    3u, 120u, // '-'
    1u, 130u, // '.'
    3u, 140u, // '/'
    5u, 150u, // '0'
    3u, 160u, // '1'
    3u, 170u, // '2'
    4u, 180u, // '3'
    5u, 190u, // '4'
    4u, 200u, // '5'
    4u, 210u, // '6'
    4u, 220u, // '7'
    4u, 230u, // '8'
    4u, 240u, // '9'
    1u, 250u, // ':'
    2u, 260u, // ';'
    2u, 270u, // '<'
    3u, 280u, // '='
    3u, 290u, // '>'
    4u, 300u, // '?'
    6u, 310u, // '@'
    5u, 320u, // 'A'
    4u, 330u, // 'B'
    4u, 340u, // 'C'
    5u, 350u, // 'D'
    4u, 360u, // 'E'
    4u, 370u, // 'F'
    5u, 380u, // 'G'
    5u, 390u, // 'H'
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
};

const dura_lcd_font_asset_t dura_font_ui_main_menu_10 = {
    "dura_font_ui_main_menu_10",
    33u,
    94u,
    10u,
    2u,
    dura_asset_comicSansMS6ptCharBitmaps,
    sizeof(dura_asset_comicSansMS6ptCharBitmaps),
    dura_asset_comicSansMS6ptCharDescriptors,
    sizeof(dura_asset_comicSansMS6ptCharDescriptors) / sizeof(dura_asset_comicSansMS6ptCharDescriptors[0]),
};

// Source: fontComicSans16.mbas const comicSansMS16ptCharBitmaps as byte[11*2*17 + 2*1*17] (374 values)
const uint8_t dura_asset_comicSansMS16ptCharBitmaps[374] = {
    0x00u, 0x00u, 0x00u, 0x00u, 0x00u, 0x00u, 0x00u, 0x00u, 0x00u, 0x00u, 0x00u, 0x00u, 0x00u, 0xC0u, 0xC0u, 0xC0u,
    0x00u, 0x01u, 0x80u, 0x01u, 0x80u, 0x03u, 0x00u, 0x03u, 0x00u, 0x07u, 0x00u, 0x06u, 0x00u, 0x06u, 0x00u, 0x0Cu,
    0x00u, 0x0Cu, 0x00u, 0x18u, 0x00u, 0x38u, 0x00u, 0x30u, 0x00u, 0x70u, 0x00u, 0x60u, 0x00u, 0x60u, 0x00u, 0xC0u,
    0x00u, 0xC0u, 0x00u, 0x0Fu, 0x00u, 0x3Fu, 0x80u, 0x71u, 0xC0u, 0x60u, 0xC0u, 0xE0u, 0x60u, 0xC0u, 0x60u, 0xC0u,
    0x60u, 0xC0u, 0x60u, 0xC0u, 0x60u, 0xC0u, 0x60u, 0xC0u, 0x60u, 0xE0u, 0xE0u, 0x60u, 0xC0u, 0x71u, 0xC0u, 0x3Fu,
    0x80u, 0x1Fu, 0x00u, 0x00u, 0x00u, 0x30u, 0x70u, 0xF0u, 0xB0u, 0x30u, 0x30u, 0x30u, 0x30u, 0x30u, 0x30u, 0x30u,
    0x30u, 0x30u, 0x30u, 0xFCu, 0xFCu, 0x00u, 0x1Eu, 0x00u, 0x7Fu, 0x00u, 0xE3u, 0x80u, 0xC1u, 0x80u, 0x01u, 0x80u,
    0x01u, 0x80u, 0x03u, 0x00u, 0x0Fu, 0x00u, 0x1Cu, 0x00u, 0x38u, 0x00u, 0x70u, 0x00u, 0xE0u, 0x00u, 0xC0u, 0x00u,
    0xC0u, 0x00u, 0xFFu, 0x80u, 0xFFu, 0x80u, 0x00u, 0x00u, 0x1Fu, 0x00u, 0x7Fu, 0x80u, 0x61u, 0xC0u, 0x00u, 0xC0u,
    0x00u, 0xC0u, 0x01u, 0xC0u, 0x0Fu, 0x80u, 0x1Fu, 0x00u, 0x03u, 0x80u, 0x01u, 0xC0u, 0x00u, 0xC0u, 0x00u, 0xC0u,
    0xC0u, 0xC0u, 0xE1u, 0x80u, 0x7Fu, 0x80u, 0x3Eu, 0x00u, 0x00u, 0x00u, 0x01u, 0x80u, 0x03u, 0x80u, 0x07u, 0x80u,
    0x05u, 0x80u, 0x0Du, 0x80u, 0x19u, 0x80u, 0x19u, 0x80u, 0x31u, 0x80u, 0x31u, 0x80u, 0x61u, 0x80u, 0xFFu, 0xE0u,
    0xFFu, 0xE0u, 0x01u, 0x80u, 0x01u, 0x80u, 0x01u, 0x80u, 0x01u, 0x80u, 0x00u, 0x00u, 0xFFu, 0xC0u, 0xFFu, 0xC0u,
    0x60u, 0x00u, 0xC0u, 0x00u, 0xDFu, 0x00u, 0xFFu, 0xC0u, 0xF0u, 0xC0u, 0xE0u, 0x60u, 0xC0u, 0x60u, 0x00u, 0x60u,
    0x00u, 0x60u, 0x00u, 0x60u, 0xC0u, 0xC0u, 0xE1u, 0xC0u, 0x7Fu, 0x80u, 0x3Eu, 0x00u, 0x00u, 0x00u, 0x03u, 0x00u,
    0x07u, 0x00u, 0x1Eu, 0x00u, 0x18u, 0x00u, 0x30u, 0x00u, 0x60u, 0x00u, 0x7Fu, 0x00u, 0xFFu, 0xC0u, 0xE0u, 0xE0u,
    0xC0u, 0x60u, 0xC0u, 0x60u, 0xC0u, 0x60u, 0xE0u, 0xE0u, 0x71u, 0xC0u, 0x7Fu, 0x80u, 0x1Fu, 0x00u, 0x00u, 0x00u,
    0xFFu, 0xF0u, 0xFFu, 0xF0u, 0x00u, 0xE0u, 0x01u, 0xC0u, 0x01u, 0x80u, 0x03u, 0x80u, 0x03u, 0x00u, 0x07u, 0x00u,
    0x06u, 0x00u, 0x0Eu, 0x00u, 0x0Cu, 0x00u, 0x0Cu, 0x00u, 0x1Cu, 0x00u, 0x18u, 0x00u, 0x38u, 0x00u, 0x30u, 0x00u,
    0x00u, 0x00u, 0x1Fu, 0x00u, 0x7Fu, 0x80u, 0xE1u, 0xC0u, 0xC0u, 0xC0u, 0xC0u, 0xC0u, 0xE1u, 0xC0u, 0x7Fu, 0x80u,
    0x3Fu, 0x80u, 0x73u, 0x80u, 0xE1u, 0xC0u, 0xC0u, 0xC0u, 0xC0u, 0xC0u, 0xC0u, 0xC0u, 0xE1u, 0xC0u, 0x7Fu, 0x80u,
    0x3Eu, 0x00u, 0x00u, 0x00u, 0x1Fu, 0x00u, 0x3Fu, 0x80u, 0x61u, 0xC0u, 0xC0u, 0xE0u, 0xC0u, 0x60u, 0xC0u, 0x60u,
    0xC0u, 0x60u, 0xC0u, 0x60u, 0x61u, 0xE0u, 0x7Fu, 0xC0u, 0x1Eu, 0xC0u, 0x00u, 0xC0u, 0x01u, 0x80u, 0x03u, 0x00u,
    0x0Eu, 0x00u, 0x7Cu, 0x00u, 0x70u, 0x00u
};

// Source: fontComicSans16.mbas const comicSansMS16ptCharDescriptors as word[12*2] (24 values)
const uint16_t dura_asset_comicSansMS16ptCharDescriptors[24] = {
    2u, 0u, 9u, 17u, 11u, 51u, 6u, 85u, 9u, 102u, 10u, 136u,
    11u, 170u, 11u, 204u, 11u, 238u, 12u, 272u, 10u, 306u, 11u, 340u
};

// Source: fontArialNumbers24.mbas const arialNarrow24ptCharBitmaps as byte[14*23+14*20] (552 values)
const uint8_t dura_asset_arialNarrow24ptCharBitmaps[552] = {
    0x00u, 0x00u, 0x00u, 0x00u, 0x00u, 0x00u, 0x00u, 0x00u, 0x00u, 0x00u, 0x00u, 0x00u, 0x00u, 0x00u, 0x00u, 0x00u,
    0x00u, 0x00u, 0x00u, 0xF0u, 0xF0u, 0xF0u, 0xF0u, 0x0Eu, 0x0Eu, 0x0Eu, 0x1Cu, 0x1Cu, 0x1Cu, 0x1Cu, 0x1Cu, 0x3Cu,
    0x38u, 0x38u, 0x38u, 0x38u, 0x38u, 0x78u, 0x70u, 0x70u, 0x70u, 0x70u, 0x70u, 0xE0u, 0xE0u, 0xE0u, 0x0Fu, 0x80u,
    0x1Fu, 0xC0u, 0x3Fu, 0xE0u, 0x7Fu, 0xF0u, 0x78u, 0xF0u, 0x78u, 0xF0u, 0xF0u, 0x78u, 0xF0u, 0x78u, 0xF0u, 0x78u,
    0xF0u, 0x78u, 0xF0u, 0x78u, 0xF0u, 0x78u, 0xF0u, 0x78u, 0xF0u, 0x78u, 0xF0u, 0x78u, 0xF0u, 0x78u, 0xF0u, 0x78u,
    0x78u, 0xF0u, 0x78u, 0xF0u, 0x7Fu, 0xF0u, 0x3Fu, 0xE0u, 0x1Fu, 0xC0u, 0x0Fu, 0x80u, 0x03u, 0x80u, 0x07u, 0x80u,
    0x0Fu, 0x80u, 0x1Fu, 0x80u, 0x7Fu, 0x80u, 0xFFu, 0x80u, 0xF7u, 0x80u, 0xE7u, 0x80u, 0x87u, 0x80u, 0x07u, 0x80u,
    0x07u, 0x80u, 0x07u, 0x80u, 0x07u, 0x80u, 0x07u, 0x80u, 0x07u, 0x80u, 0x07u, 0x80u, 0x07u, 0x80u, 0x07u, 0x80u,
    0x07u, 0x80u, 0x07u, 0x80u, 0x07u, 0x80u, 0x07u, 0x80u, 0x07u, 0x80u, 0x0Fu, 0x80u, 0x3Fu, 0xE0u, 0x7Fu, 0xF0u,
    0x7Fu, 0xF0u, 0xF8u, 0xF8u, 0xF0u, 0x78u, 0xF0u, 0x78u, 0x00u, 0x78u, 0x00u, 0x78u, 0x00u, 0xF0u, 0x00u, 0xF0u,
    0x01u, 0xF0u, 0x03u, 0xE0u, 0x07u, 0xC0u, 0x0Fu, 0x80u, 0x1Fu, 0x00u, 0x1Eu, 0x00u, 0x3Cu, 0x00u, 0x7Cu, 0x00u,
    0x7Fu, 0xF8u, 0x7Fu, 0xF8u, 0xFFu, 0xF8u, 0xFFu, 0xF8u, 0x0Fu, 0x80u, 0x3Fu, 0xE0u, 0x3Fu, 0xF0u, 0x7Fu, 0xF0u,
    0x78u, 0xF8u, 0xF0u, 0x78u, 0xF0u, 0x78u, 0x00u, 0x78u, 0x00u, 0xF0u, 0x07u, 0xF0u, 0x07u, 0xE0u, 0x07u, 0xE0u,
    0x07u, 0xF0u, 0x00u, 0xF8u, 0x00u, 0x78u, 0x00u, 0x78u, 0xF0u, 0x78u, 0xF0u, 0x78u, 0x78u, 0xF8u, 0x7Fu, 0xF0u,
    0x3Fu, 0xF0u, 0x3Fu, 0xE0u, 0x0Fu, 0x80u, 0x00u, 0xF0u, 0x00u, 0xF0u, 0x01u, 0xF0u, 0x03u, 0xF0u, 0x03u, 0xF0u,
    0x07u, 0xF0u, 0x07u, 0xF0u, 0x0Eu, 0xF0u, 0x1Eu, 0xF0u, 0x1Cu, 0xF0u, 0x3Cu, 0xF0u, 0x38u, 0xF0u, 0x70u, 0xF0u,
    0xF0u, 0xF0u, 0xFFu, 0xFCu, 0xFFu, 0xFCu, 0xFFu, 0xFCu, 0xFFu, 0xFCu, 0x00u, 0xF0u, 0x00u, 0xF0u, 0x00u, 0xF0u,
    0x00u, 0xF0u, 0x00u, 0xF0u, 0x3Fu, 0xF0u, 0x3Fu, 0xF0u, 0x3Fu, 0xF0u, 0x7Fu, 0xF0u, 0x78u, 0x00u, 0x78u, 0x00u,
    0x78u, 0x00u, 0x7Bu, 0x80u, 0x7Fu, 0xE0u, 0x7Fu, 0xF0u, 0xFFu, 0xF0u, 0xF0u, 0xF8u, 0xE0u, 0x78u, 0x00u, 0x78u,
    0x00u, 0x78u, 0x00u, 0x78u, 0xF0u, 0x78u, 0xF0u, 0x78u, 0x78u, 0xF0u, 0x7Fu, 0xF0u, 0x3Fu, 0xE0u, 0x3Fu, 0xC0u,
    0x0Fu, 0x80u, 0x07u, 0xC0u, 0x1Fu, 0xE0u, 0x3Fu, 0xF0u, 0x3Fu, 0xF0u, 0x78u, 0xF8u, 0x78u, 0x78u, 0xF0u, 0x00u,
    0xF0u, 0x00u, 0xF7u, 0x80u, 0xFFu, 0xE0u, 0xFFu, 0xF0u, 0xFFu, 0xF0u, 0xF8u, 0xF8u, 0xF0u, 0x78u, 0xF0u, 0x78u,
    0xF0u, 0x78u, 0xF0u, 0x78u, 0x70u, 0x78u, 0x78u, 0xF8u, 0x7Fu, 0xF0u, 0x3Fu, 0xF0u, 0x1Fu, 0xE0u, 0x0Fu, 0x80u,
    0xFFu, 0xF8u, 0xFFu, 0xF8u, 0xFFu, 0xF8u, 0xFFu, 0xF8u, 0x00u, 0xF0u, 0x01u, 0xE0u, 0x01u, 0xE0u, 0x03u, 0xC0u,
    0x03u, 0xC0u, 0x07u, 0x80u, 0x07u, 0x80u, 0x0Fu, 0x00u, 0x0Fu, 0x00u, 0x0Fu, 0x00u, 0x1Eu, 0x00u, 0x1Eu, 0x00u,
    0x1Eu, 0x00u, 0x1Eu, 0x00u, 0x3Cu, 0x00u, 0x3Cu, 0x00u, 0x3Cu, 0x00u, 0x3Cu, 0x00u, 0x3Cu, 0x00u, 0x0Fu, 0x80u,
    0x3Fu, 0xE0u, 0x7Fu, 0xF0u, 0xFFu, 0xF8u, 0xF8u, 0xF8u, 0xF0u, 0x78u, 0xF0u, 0x78u, 0xF0u, 0x78u, 0x78u, 0xF0u,
    0x7Fu, 0xF0u, 0x1Fu, 0xE0u, 0x3Fu, 0xE0u, 0x7Fu, 0xF0u, 0x78u, 0xF0u, 0xF0u, 0x78u, 0xF0u, 0x78u, 0xF0u, 0x78u,
    0xF0u, 0x78u, 0xF8u, 0xF8u, 0x7Fu, 0xF0u, 0x7Fu, 0xF0u, 0x3Fu, 0xE0u, 0x0Fu, 0x80u, 0x0Fu, 0x80u, 0x3Fu, 0xC0u,
    0x7Fu, 0xE0u, 0x7Fu, 0xF0u, 0xF8u, 0xF0u, 0xF0u, 0x70u, 0xF0u, 0x78u, 0xF0u, 0x78u, 0xF0u, 0x78u, 0xF0u, 0x78u,
    0xF8u, 0xF8u, 0x7Fu, 0xF8u, 0x7Fu, 0xF8u, 0x3Fu, 0xF8u, 0x0Fu, 0x78u, 0x00u, 0x78u, 0x00u, 0x78u, 0xF0u, 0xF0u,
    0xF8u, 0xF0u, 0x7Fu, 0xE0u, 0x7Fu, 0xE0u, 0x3Fu, 0xC0u, 0x1Fu, 0x00u, 0x00u, 0x00u, 0x00u, 0x00u, 0x00u, 0x00u,
    0xF0u, 0xF0u, 0xF0u, 0xF0u, 0x00u, 0x00u, 0x00u, 0x00u, 0x00u, 0x00u, 0x00u, 0x00u, 0x00u, 0xF0u, 0xF0u, 0xF0u,
    0xF0u, 0x00u, 0x00u, 0x00u, 0x00u, 0x00u, 0x00u, 0x00u, 0x00u, 0x00u, 0x00u, 0x00u, 0x00u, 0x00u, 0x00u, 0x00u,
    0x00u, 0x00u, 0x00u, 0x00u, 0x00u, 0x00u, 0x00u, 0x00u
};

// Source: fontArialNumbers24.mbas const arialNarrow24ptCharDescriptors as word[30] (30 values)
const uint16_t dura_asset_arialNarrow24ptCharDescriptors[30] = {
    4u, 0u, 7u, 23u, 13u, 46u, 9u, 92u, 13u, 138u, 13u, 184u,
    14u, 230u, 13u, 276u, 13u, 322u, 13u, 368u, 13u, 414u, 13u, 460u,
    4u, 506u, 14u, 552u, 9u, 552u
};

// Source: fontArialNumbers40.mbas const arialNarrow40ptCharBitmaps as byte[10*3*40+2*1*40+2*1*40] (1360 values)
const uint8_t dura_asset_arialNarrow40ptCharBitmaps[1360] = {
    0x00u, 0x00u, 0x00u, 0x00u, 0x00u, 0x00u, 0x00u, 0x00u, 0x00u, 0x00u, 0x00u, 0x00u, 0x00u, 0x00u, 0x00u, 0x00u,
    0x00u, 0x00u, 0x00u, 0x00u, 0x00u, 0x00u, 0x00u, 0x00u, 0x00u, 0x00u, 0x00u, 0x00u, 0x00u, 0x00u, 0x00u, 0x00u,
    0x00u, 0x00u, 0xF0u, 0xF0u, 0xF0u, 0xF0u, 0xF0u, 0x00u, 0x00u, 0x00u, 0x00u, 0x70u, 0x00u, 0x70u, 0x00u, 0x70u,
    0x00u, 0x70u, 0x00u, 0xE0u, 0x00u, 0xE0u, 0x00u, 0xE0u, 0x00u, 0xE0u, 0x01u, 0xC0u, 0x01u, 0xC0u, 0x01u, 0xC0u,
    0x01u, 0xC0u, 0x03u, 0xC0u, 0x03u, 0x80u, 0x03u, 0x80u, 0x03u, 0x80u, 0x07u, 0x80u, 0x07u, 0x00u, 0x07u, 0x00u,
    0x07u, 0x00u, 0x07u, 0x00u, 0x0Eu, 0x00u, 0x0Eu, 0x00u, 0x0Eu, 0x00u, 0x0Eu, 0x00u, 0x1Cu, 0x00u, 0x1Cu, 0x00u,
    0x1Cu, 0x00u, 0x1Cu, 0x00u, 0x38u, 0x00u, 0x38u, 0x00u, 0x38u, 0x00u, 0x38u, 0x00u, 0x78u, 0x00u, 0x70u, 0x00u,
    0x70u, 0x00u, 0x70u, 0x00u, 0xF0u, 0x00u, 0xE0u, 0x00u, 0x01u, 0xF8u, 0x00u, 0x07u, 0xFEu, 0x00u, 0x0Fu, 0xFFu,
    0x00u, 0x1Fu, 0xFFu, 0x80u, 0x1Fu, 0x0Fu, 0x80u, 0x3Eu, 0x07u, 0xC0u, 0x3Cu, 0x03u, 0xC0u, 0x3Cu, 0x03u, 0xC0u,
    0x78u, 0x01u, 0xE0u, 0x78u, 0x01u, 0xE0u, 0x78u, 0x01u, 0xE0u, 0x78u, 0x01u, 0xE0u, 0xF0u, 0x00u, 0xF0u, 0xF0u,
    0x00u, 0xF0u, 0xF0u, 0x00u, 0xF0u, 0xF0u, 0x00u, 0xF0u, 0xF0u, 0x00u, 0xF0u, 0xF0u, 0x00u, 0xF0u, 0xF0u, 0x00u,
    0xF0u, 0xF0u, 0x00u, 0xF0u, 0xF0u, 0x00u, 0xF0u, 0xF0u, 0x00u, 0xF0u, 0xF0u, 0x00u, 0xF0u, 0xF0u, 0x00u, 0xF0u,
    0xF0u, 0x00u, 0xF0u, 0xF0u, 0x00u, 0xF0u, 0xF0u, 0x00u, 0xF0u, 0x78u, 0x01u, 0xE0u, 0x78u, 0x01u, 0xE0u, 0x78u,
    0x01u, 0xE0u, 0x78u, 0x01u, 0xE0u, 0x7Cu, 0x03u, 0xC0u, 0x3Cu, 0x03u, 0xC0u, 0x3Eu, 0x07u, 0xC0u, 0x1Fu, 0x0Fu,
    0x80u, 0x1Fu, 0xFFu, 0x80u, 0x0Fu, 0xFFu, 0x00u, 0x07u, 0xFEu, 0x00u, 0x01u, 0xF8u, 0x00u, 0x00u, 0x00u, 0x00u,
    0x00u, 0x07u, 0x00u, 0x00u, 0x07u, 0x00u, 0x00u, 0x0Fu, 0x00u, 0x00u, 0x1Fu, 0x00u, 0x00u, 0x1Fu, 0x00u, 0x00u,
    0x3Fu, 0x00u, 0x00u, 0x7Fu, 0x00u, 0x00u, 0xFFu, 0x00u, 0x03u, 0xFFu, 0x00u, 0x07u, 0xEFu, 0x00u, 0x0Fu, 0x8Fu,
    0x00u, 0x0Fu, 0x0Fu, 0x00u, 0x0Eu, 0x0Fu, 0x00u, 0x08u, 0x0Fu, 0x00u, 0x00u, 0x0Fu, 0x00u, 0x00u, 0x0Fu, 0x00u,
    0x00u, 0x0Fu, 0x00u, 0x00u, 0x0Fu, 0x00u, 0x00u, 0x0Fu, 0x00u, 0x00u, 0x0Fu, 0x00u, 0x00u, 0x0Fu, 0x00u, 0x00u,
    0x0Fu, 0x00u, 0x00u, 0x0Fu, 0x00u, 0x00u, 0x0Fu, 0x00u, 0x00u, 0x0Fu, 0x00u, 0x00u, 0x0Fu, 0x00u, 0x00u, 0x0Fu,
    0x00u, 0x00u, 0x0Fu, 0x00u, 0x00u, 0x0Fu, 0x00u, 0x00u, 0x0Fu, 0x00u, 0x00u, 0x0Fu, 0x00u, 0x00u, 0x0Fu, 0x00u,
    0x00u, 0x0Fu, 0x00u, 0x00u, 0x0Fu, 0x00u, 0x00u, 0x0Fu, 0x00u, 0x00u, 0x0Fu, 0x00u, 0x00u, 0x0Fu, 0x00u, 0x00u,
    0x0Fu, 0x00u, 0x00u, 0x0Fu, 0x00u, 0x00u, 0x00u, 0x00u, 0x01u, 0xFCu, 0x00u, 0x07u, 0xFFu, 0x00u, 0x0Fu, 0xFFu,
    0x80u, 0x1Fu, 0xFFu, 0xC0u, 0x1Fu, 0x07u, 0xC0u, 0x3Eu, 0x03u, 0xE0u, 0x3Cu, 0x01u, 0xE0u, 0x3Cu, 0x01u, 0xF0u,
    0x78u, 0x00u, 0xF0u, 0x78u, 0x00u, 0xF0u, 0x78u, 0x00u, 0xF0u, 0x00u, 0x00u, 0xF0u, 0x00u, 0x00u, 0xF0u, 0x00u,
    0x00u, 0xF0u, 0x00u, 0x01u, 0xF0u, 0x00u, 0x01u, 0xE0u, 0x00u, 0x03u, 0xE0u, 0x00u, 0x03u, 0xC0u, 0x00u, 0x07u,
    0xC0u, 0x00u, 0x0Fu, 0x80u, 0x00u, 0x0Fu, 0x80u, 0x00u, 0x1Fu, 0x00u, 0x00u, 0x3Eu, 0x00u, 0x00u, 0x7Cu, 0x00u,
    0x00u, 0xF8u, 0x00u, 0x01u, 0xF8u, 0x00u, 0x03u, 0xF0u, 0x00u, 0x07u, 0xE0u, 0x00u, 0x07u, 0xC0u, 0x00u, 0x0Fu,
    0x80u, 0x00u, 0x1Fu, 0x00u, 0x00u, 0x3Eu, 0x00u, 0x00u, 0x3Cu, 0x00u, 0x00u, 0x7Cu, 0x00u, 0x00u, 0x78u, 0x00u,
    0x00u, 0x7Fu, 0xFFu, 0xF0u, 0xFFu, 0xFFu, 0xF0u, 0xFFu, 0xFFu, 0xF0u, 0xFFu, 0xFFu, 0xF0u, 0x00u, 0x00u, 0x00u,
    0x01u, 0xF8u, 0x00u, 0x07u, 0xFEu, 0x00u, 0x0Fu, 0xFFu, 0x00u, 0x1Fu, 0xFFu, 0x80u, 0x3Fu, 0x0Fu, 0xC0u, 0x3Eu,
    0x03u, 0xC0u, 0x3Cu, 0x03u, 0xC0u, 0x78u, 0x01u, 0xE0u, 0x78u, 0x01u, 0xE0u, 0x00u, 0x01u, 0xE0u, 0x00u, 0x01u,
    0xE0u, 0x00u, 0x01u, 0xE0u, 0x00u, 0x01u, 0xE0u, 0x00u, 0x03u, 0xC0u, 0x00u, 0x07u, 0xC0u, 0x00u, 0x1Fu, 0x80u,
    0x00u, 0xFFu, 0x80u, 0x00u, 0xFFu, 0x00u, 0x01u, 0xFFu, 0x00u, 0x01u, 0xFFu, 0x80u, 0x00u, 0x0Fu, 0xC0u, 0x00u,
    0x03u, 0xE0u, 0x00u, 0x01u, 0xE0u, 0x00u, 0x01u, 0xE0u, 0x00u, 0x00u, 0xF0u, 0x00u, 0x00u, 0xF0u, 0x00u, 0x00u,
    0xF0u, 0x00u, 0x00u, 0xF0u, 0xF0u, 0x00u, 0xF0u, 0xF0u, 0x00u, 0xF0u, 0xF8u, 0x01u, 0xF0u, 0x78u, 0x01u, 0xE0u,
    0x78u, 0x03u, 0xE0u, 0x7Cu, 0x07u, 0xC0u, 0x3Fu, 0x0Fu, 0xC0u, 0x1Fu, 0xFFu, 0x80u, 0x0Fu, 0xFFu, 0x00u, 0x07u,
    0xFEu, 0x00u, 0x01u, 0xF8u, 0x00u, 0x00u, 0x00u, 0x00u, 0x00u, 0x0Fu, 0x80u, 0x00u, 0x0Fu, 0x80u, 0x00u, 0x1Fu,
    0x80u, 0x00u, 0x1Fu, 0x80u, 0x00u, 0x3Fu, 0x80u, 0x00u, 0x3Fu, 0x80u, 0x00u, 0x7Fu, 0x80u, 0x00u, 0x7Fu, 0x80u,
    0x00u, 0xFFu, 0x80u, 0x00u, 0xF7u, 0x80u, 0x01u, 0xF7u, 0x80u, 0x01u, 0xE7u, 0x80u, 0x03u, 0xE7u, 0x80u, 0x03u,
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
};

// Source: fontArialNumbers40.mbas const arialNarrow40ptCharDescriptors as word[26] (26 values)
const uint16_t dura_asset_arialNarrow40ptCharDescriptors[26] = {
    4u, 0u, 12u, 40u, 20u, 120u, 20u, 240u, 20u, 360u, 20u, 480u,
    20u, 600u, 20u, 720u, 20u, 840u, 20u, 960u, 20u, 1080u, 20u, 1200u,
    4u, 1320u
};

// Bitmap asset descriptors
const dura_lcd_bitmap_asset_t dura_bitmap_QRcodeData = { 128u, 64u, dura_asset_QRcodeData, sizeof(dura_asset_QRcodeData), "QRcodeData" }; // Full-screen QR code bitmap from Graphics.mbas
const dura_lcd_bitmap_asset_t dura_bitmap_durametertitle_bmp_glcd_bmp = { 128u, 8u, dura_asset_durametertitle_bmp_glcd_bmp, sizeof(dura_asset_durametertitle_bmp_glcd_bmp), "durametertitle_bmp_glcd_bmp" }; // Dura-Meter title bitmap from Graphics.mbas
const dura_lcd_bitmap_asset_t dura_bitmap_logoData = { 128u, 64u, dura_asset_logoData, sizeof(dura_asset_logoData), "logoData" }; // Dura full-screen boot logo/splash bitmap from Graphics.mbas
const dura_lcd_bitmap_asset_t dura_bitmap_battery_icon_glcd_bmp = { 15u, 32u, dura_asset_battery_icon_glcd_bmp, sizeof(dura_asset_battery_icon_glcd_bmp), "battery_icon_glcd_bmp" }; // Battery icon bitmap; legacy declaration is byte[(32*15)/8] but draw calls use width=15 height=32
const dura_lcd_bitmap_asset_t dura_bitmap_thick_glcd_bmp = { 17u, 5u, dura_asset_thick_glcd_bmp, sizeof(dura_asset_thick_glcd_bmp), "thick_glcd_bmp" }; // THICK text/icon bitmap from Graphics.mbas
const dura_lcd_bitmap_asset_t dura_bitmap_thin_glcd_bmp = { 13u, 5u, dura_asset_thin_glcd_bmp, sizeof(dura_asset_thin_glcd_bmp), "thin_glcd_bmp" }; // THIN text/icon bitmap from Graphics.mbas
const dura_lcd_bitmap_asset_t dura_bitmap_thick_pointer = { 7u, 5u, dura_asset_thick_pointer, sizeof(dura_asset_thick_pointer), "thick_pointer" }; // 7x5 thick pointer bitmap from Graphics.mbas

// Font asset descriptors
const dura_lcd_font_asset_t dura_font_legacy_5x7 = { "dura_font_legacy_5x7", 0u, 255u, 7u, 1u, dura_asset_font, sizeof(dura_asset_font), NULL, 0u }; // Legacy 5x7 fixed-width GLCD font from gLCDfont.mbas
const dura_lcd_font_asset_t dura_font_ui_small = { "dura_font_ui_small", 33u, 223u, 11u, 2u, dura_asset_comicSansMS7ptCharBitmaps, sizeof(dura_asset_comicSansMS7ptCharBitmaps), dura_asset_comicSansMS7ptCharDescriptors, (sizeof(dura_asset_comicSansMS7ptCharDescriptors) / sizeof(dura_asset_comicSansMS7ptCharDescriptors[0])) }; // Legacy small variable-width UI font from fontComicSans7.mbas
const dura_lcd_font_asset_t dura_font_ui_16 = { "dura_font_ui_16", 46u, 12u, 17u, 2u, dura_asset_comicSansMS16ptCharBitmaps, sizeof(dura_asset_comicSansMS16ptCharBitmaps), dura_asset_comicSansMS16ptCharDescriptors, (sizeof(dura_asset_comicSansMS16ptCharDescriptors) / sizeof(dura_asset_comicSansMS16ptCharDescriptors[0])) }; // Legacy Comic Sans 16pt limited numeric punctuation font from fontComicSans16.mbas
const dura_lcd_font_asset_t dura_font_num_24 = { "dura_font_num_24", 46u, 15u, 23u, 3u, dura_asset_arialNarrow24ptCharBitmaps, sizeof(dura_asset_arialNarrow24ptCharBitmaps), dura_asset_arialNarrow24ptCharDescriptors, (sizeof(dura_asset_arialNarrow24ptCharDescriptors) / sizeof(dura_asset_arialNarrow24ptCharDescriptors[0])) }; // Legacy Arial Narrow 24pt numeric font from fontArialNumbers24.mbas
const dura_lcd_font_asset_t dura_font_num_40 = { "dura_font_num_40", 46u, 13u, 40u, 3u, dura_asset_arialNarrow40ptCharBitmaps, sizeof(dura_asset_arialNarrow40ptCharBitmaps), dura_asset_arialNarrow40ptCharDescriptors, (sizeof(dura_asset_arialNarrow40ptCharDescriptors) / sizeof(dura_asset_arialNarrow40ptCharDescriptors[0])) }; // Legacy Arial Narrow 40pt numeric font from fontArialNumbers40.mbas
